cwi-dis/iotsaNeoClock/mainNeoClock.cpp

//
// An internet-connected clock, comprised of 60 NeoPixel LEDs. Shows the time,
// but can also show programmable patterns (as alerts) and temporal information
// (such as expected rainfall for the coming hour). See readme.md.
//

#include "iotsa.h"
#include "iotsaFS.h"
#include "iotsaNtp.h"
#include "iotsaFiles.h"
#include "iotsaFilesUpload.h"
#include "iotsaFilesBackup.h"

// Display + optional-feature selection. PlatformIO sets these per board via
// platformio.ini build_flags: NeoPixel for env:iotsa_v4, round LCD for
// env:crowpanel128 (an ESP32-C3, PlatformIO only -- the Arduino toolchain
// can't build iotsa for C3, see cwi-dis/iotsa#200). A plain Arduino IDE build
// has no build_flags and is always the esp8266 NeoPixel wall clock, so
// default to that here. (These flags are used only in this file.)
#if !defined(WITH_NEOPIXEL_DISPLAY) && !defined(WITH_ROUNDLCD_DISPLAY)
#define WITH_NEOPIXEL_DISPLAY
#endif
#ifndef WITH_BUIENRADAR
#define WITH_BUIENRADAR
#endif

IotsaApplication application("NeoPixel Clock Server");

// Configure modules we need
IotsaNtpMod ntpMod(application);    // we want NTP because we're a clock
IotsaFilesMod filesMod(application);// we want files mainly to share notification patterns
IotsaFilesUploadMod filesUploadMod(application);  // we want upload to set notification patterns
IotsaFilesBackupMod filesBackupMod(application);  // we want backup to clone the clock

#define NEOPIXEL_PIN      14

#define WITH_BRIGHTNESS   // Define to allow changing of the clock brightness through the web interface

#ifdef WITH_BRIGHTNESS
#include "iotsaBrightnessMod.h"
IotsaBrightnessMod brightnessMod(application);
#endif

#include "iotsaNeoClockMod.h"

#ifdef WITH_NEOPIXEL_DISPLAY
#include "NeoPixelStripDisplay.h"
NeoPixelStripDisplay neoClockDisplay(NUM_LEDS, NEOPIXEL_PIN);
#endif
#ifdef WITH_ROUNDLCD_DISPLAY
#include "CrowPanelRoundDisplay.h"
CrowPanelRoundDisplay neoClockDisplay(NUM_LEDS);
#endif

IotsaNeoClockMod neoClockMod(application, neoClockDisplay,
#ifdef WITH_BRIGHTNESS
  &brightnessMod
#else
  NULL
#endif
);

#ifdef WITH_BUIENRADAR
#include "iotsaBuienradarMod.h"
IotsaBuienradarMod buienradarMod(application, neoClockMod);
#endif

void setup(void){
  application.setup();
  application.lateSetup();
#ifndef ESP32
  ESP.wdtEnable(WDTO_120MS);
#endif
}

void loop(void){
  application.loop();
}
